siraisisatoru/10key_macro/Circuit design/SCH_10-key-marco_2024-03-20.kicad_sch

## KiCad design Circuit design/SCH_10-key-marco_2024-03-20.kicad_sch (2024-03-20)

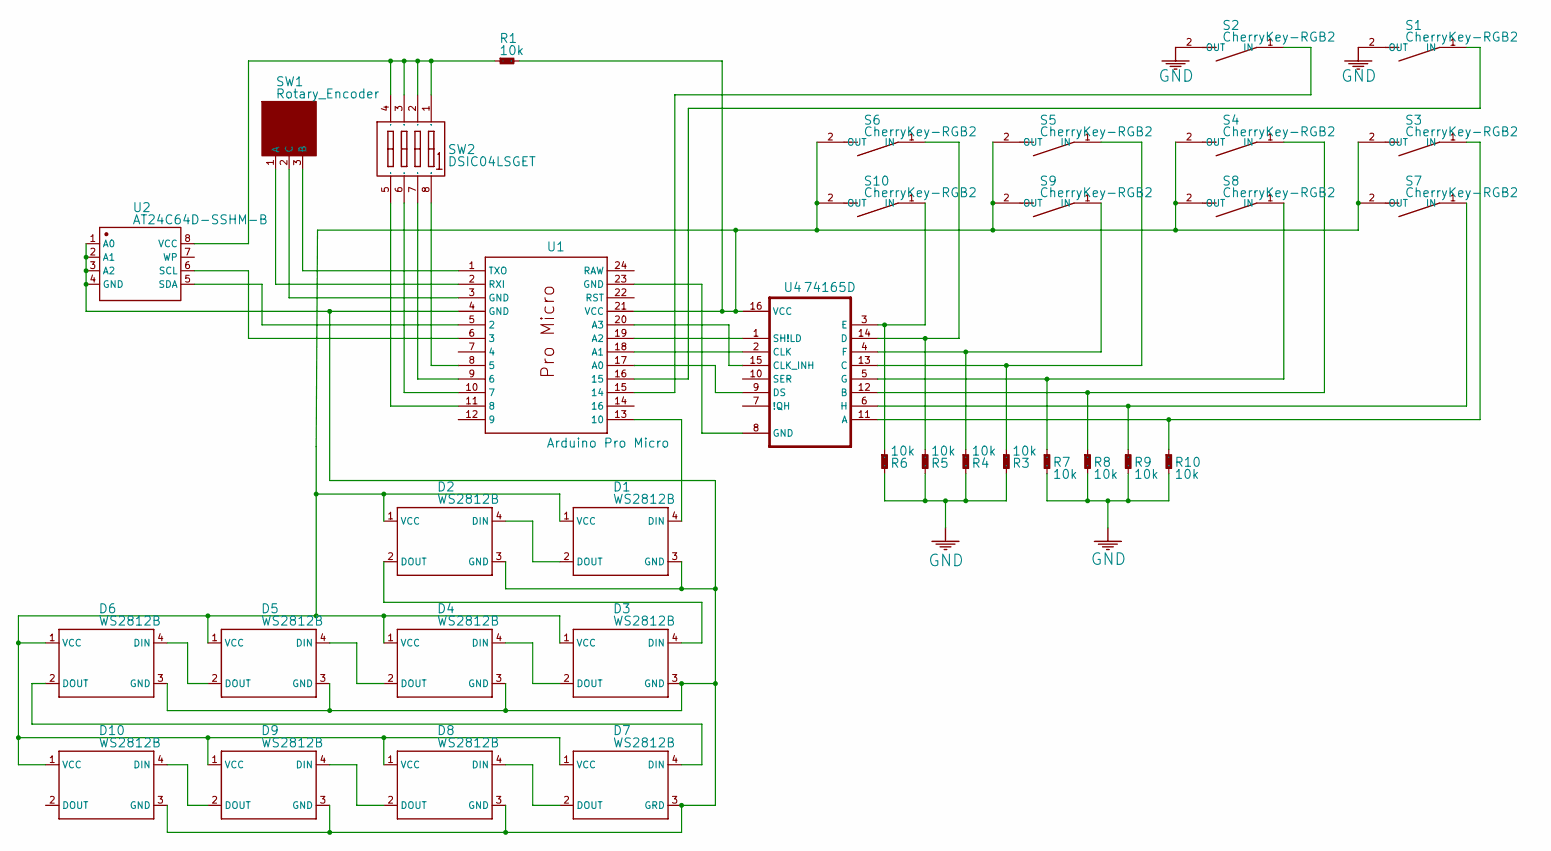
[picture p8: schematic SCH_10-key-marco_2024-03-20.kicad_sch]

Parts:
D1, D2, D3, D4, D5, D6, D7, D8, D9, D10: WS2812B
R1, R3, R4, R5, R6, R7, R8, R9, R10: 10k
S1, S2, S3, S4, S5, S6, S7, S8, S9, S10: CherryKey-RGB2
SW1: Rotary_Encoder
SW2: DSIC04LSGET
U1: Arduino Pro Micro
U2: AT24C64D-SSHM-B
U4: 74165D

Connections:
unnamed: D1.1 (VCC), D2.1 (VCC), D3.1 (VCC), D4.1 (VCC), D5.1 (VCC), D6.1 (VCC), D7.1 (VCC), D8.1 (VCC), D9.1 (VCC), D10.1 (VCC), R1.2, S3.2 (OUT), S4.2 (OUT), S5.2 (OUT), S6.2 (OUT), S7.2 (OUT), S8.2 (OUT), S9.2 (OUT), S10.2 (OUT), U1.21 (VCC), U4.16 (VCC)
unnamed: D1.2 (DOUT), D2.4 (DIN)
unnamed: D1.3 (GND), D2.3 (GND), D3.3 (GND), D4.3 (GND), D5.3 (GND), D6.3 (GND), D7.3 (GRD), D8.3 (GND), D9.3 (GND), D10.3 (GND), U1.4 (GND), U2.1 (A0), U2.2 (A1), U2.3 (A2), U2.4 (GND)
unnamed: D1.4 (DIN), U1.13 (10)
unnamed: D2.2 (DOUT), D3.4 (DIN)
unnamed: D3.2 (DOUT), D4.4 (DIN)
unnamed: D4.2 (DOUT), D5.4 (DIN)
unnamed: D5.2 (DOUT), D6.4 (DIN)
unnamed: D6.2 (DOUT), D7.4 (DIN)
unnamed: D7.2 (DOUT), D8.4 (DIN)
unnamed: D8.2 (DOUT), D9.4 (DIN)
unnamed: D9.2 (DOUT), D10.4 (DIN)
unnamed: R1.1, SW2.1 (A1), SW2.2 (A2), SW2.3 (A3), SW2.4 (A4), U2.8 (VCC)
unnamed: R3.1, S5.1 (IN), U4.13 (C)
unnamed: R3.2, R4.2, R5.2, R6.2
unnamed: R4.1, S9.1 (IN), U4.4 (F)
unnamed: R5.1, S6.1 (IN), U4.14 (D)
unnamed: R6.1, S10.1 (IN), U4.3 (E)
unnamed: R7.1, S8.1 (IN), U4.5 (G)
unnamed: R8.1, S4.1 (IN), U4.12 (B)
unnamed: R9.1, S7.1 (IN), U4.6 (H)
unnamed: R10.1, S3.1 (IN), U4.11 (A)
unnamed: R7.2, R8.2, R9.2, R10.2
unnamed: S1.1 (IN), U1.16 (15)
unnamed: S2.1 (IN), U1.15 (14)
unnamed: SW1.1 (A), U1.2 (RXI)
unnamed: SW1.2 (C), U1.3 (GND)
unnamed: SW1.3 (B), U1.1 (TXO)
unnamed: SW2.5 (B4), U1.11 (8)
unnamed: SW2.6 (B3), U1.10 (7)
unnamed: SW2.7 (B2), U1.9 (6)
unnamed: SW2.8 (B1), U1.8 (5)
unnamed: U1.5 (2), U2.5 (SDA)
unnamed: U1.6 (3), U2.6 (SCL)
unnamed: U1.17 (A0), U4.9 (DS)
unnamed: U1.18 (A1), U4.2 (CLK)
unnamed: U1.19 (A2), U4.1 (SH!LD)
unnamed: U1.20 (A3), U4.15 (CLK_INH)
unnamed: U1.23 (GND), U4.8 (GND)
